richard6534/ESP32-ArtnetSPI/Image/IMG_0633.JPG

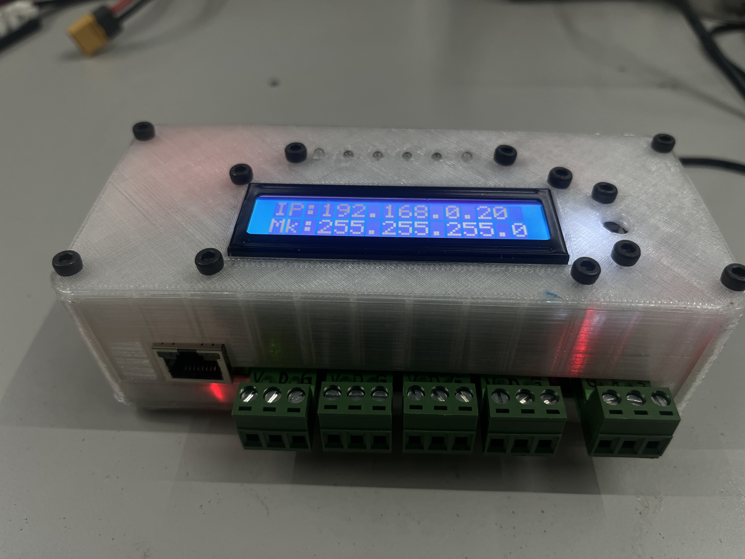
Image/IMG_0633.JPG
