richard6534/ESP32-ArtnetSPI/Image/IMG_0634.JPG

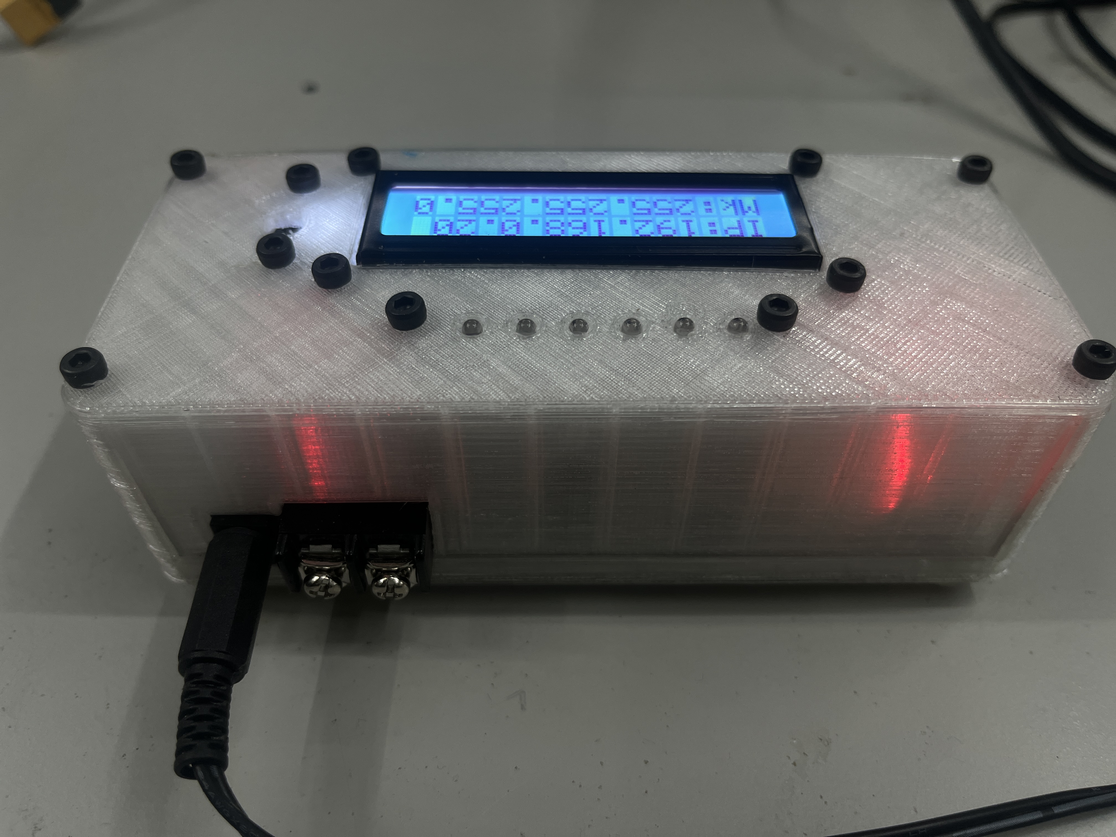
Image/IMG_0634.JPG
