richard6534/ESP32-ArtnetSPI/Image/IMG_0635.JPG

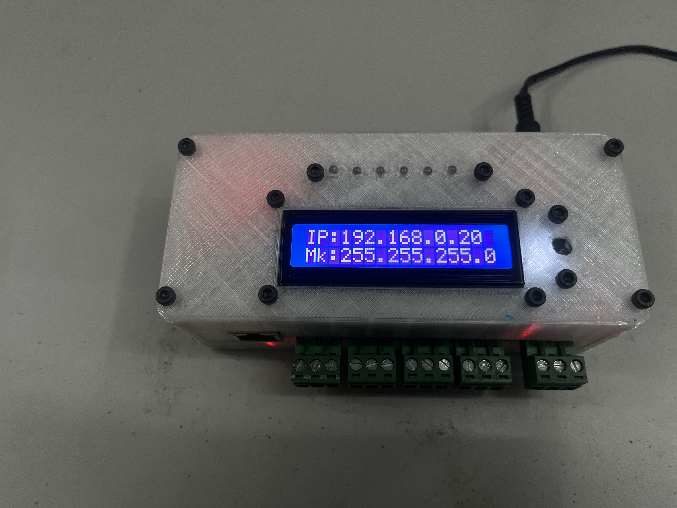
Image/IMG_0635.JPG
