richard6534/ESP32-ArtnetSPI/Image/IMG_0636.JPG

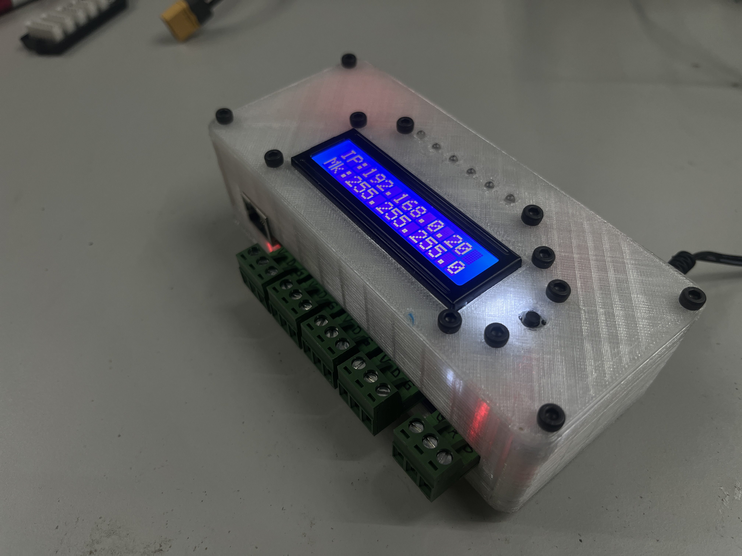
Image/IMG_0636.JPG
