richard6534/ESP32-ArtnetSPI/Image/IMG_0644.JPG

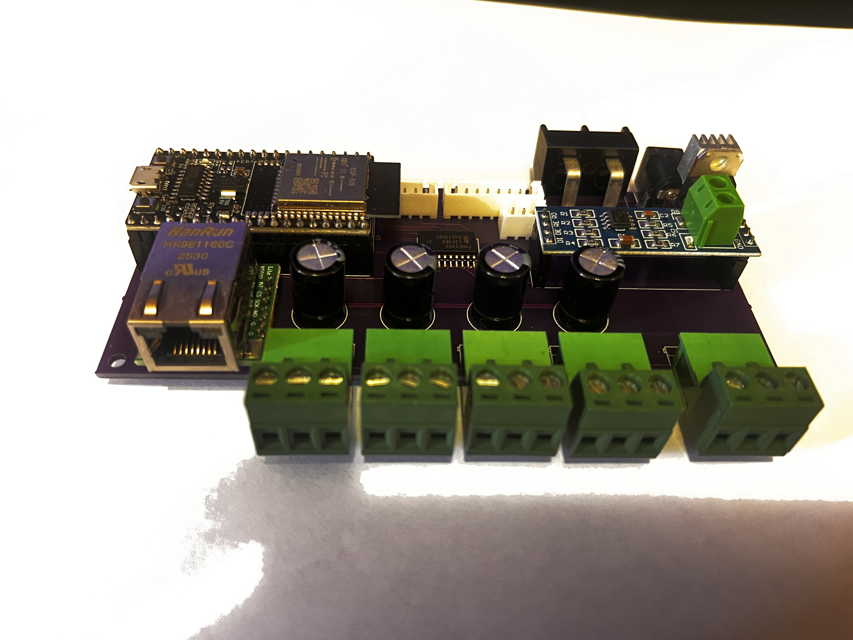
Image/IMG_0644.JPG
