richard6534/ESP32-ArtnetSPI/Image/IMG_0645.JPG

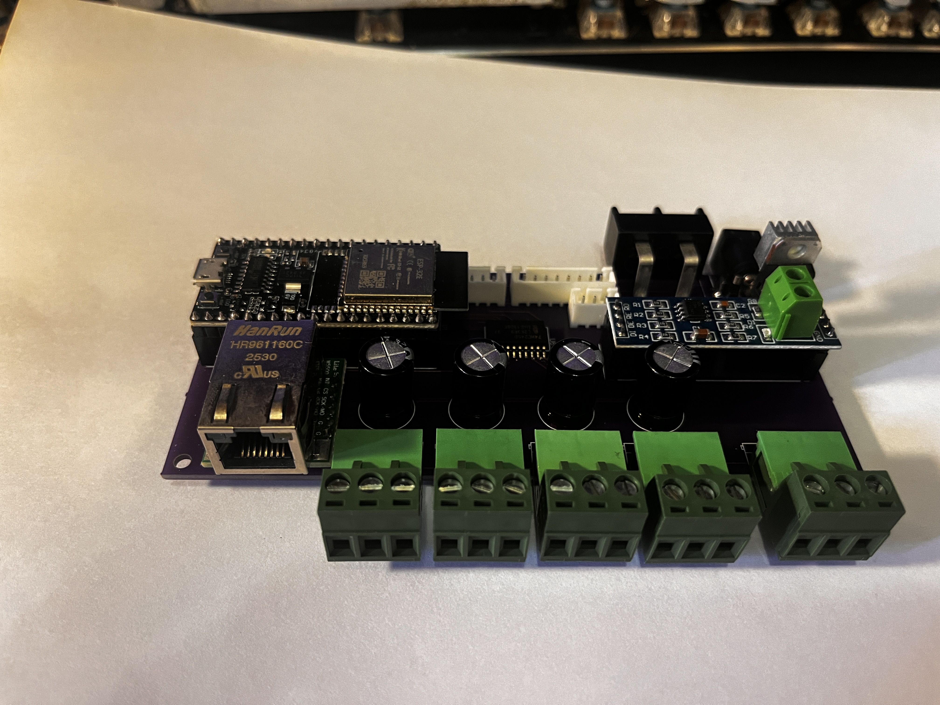
Image/IMG_0645.JPG
