richard6534/ESP32-ArtnetSPI/Image/IMG_0646.JPG

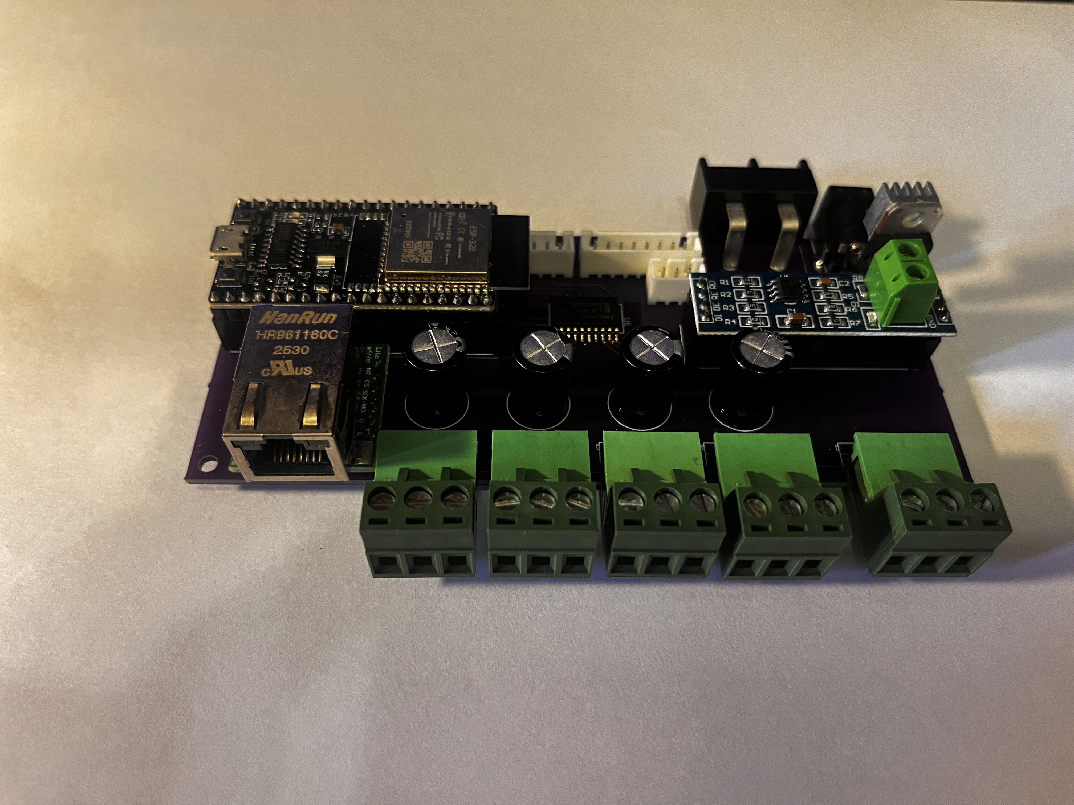
Image/IMG_0646.JPG
