richard6534/ESP32-ArtnetSPI/Image/IMG_0647.JPG

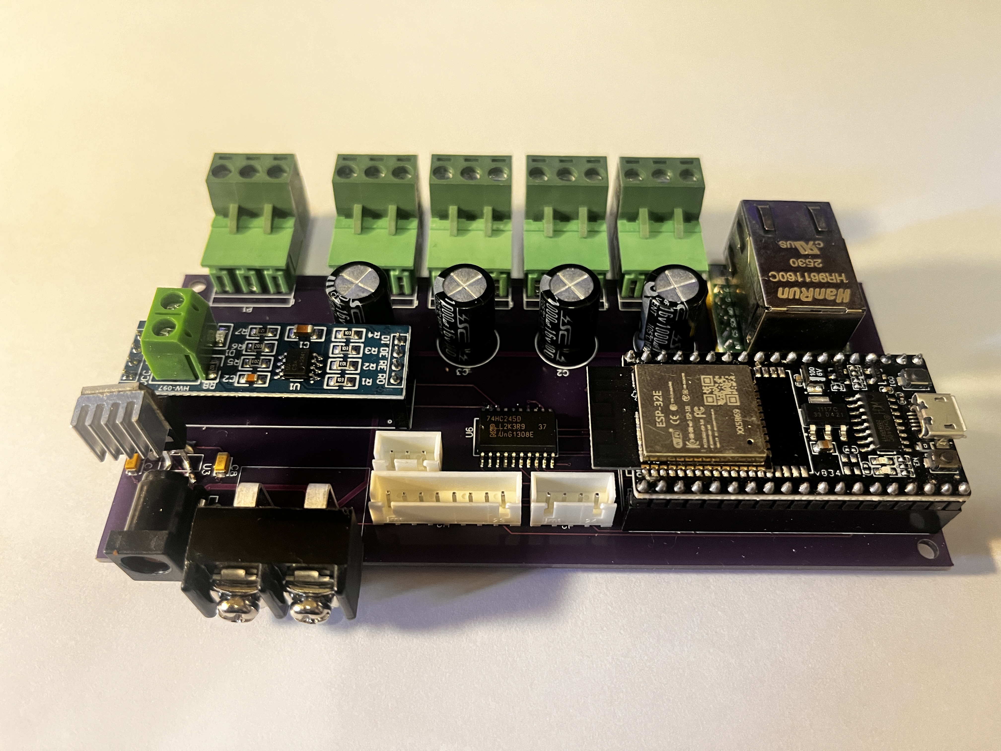
Image/IMG_0647.JPG
